xywatch/GoWatch/docs/1device选项.png

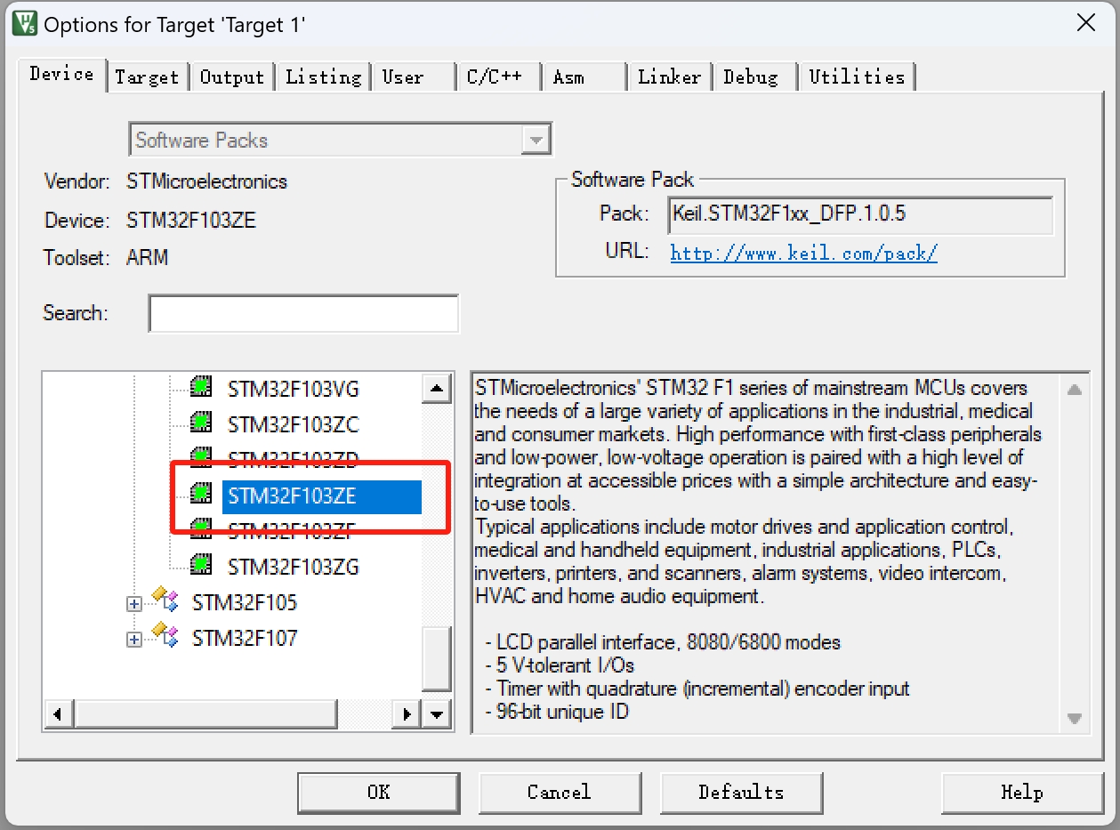
docs/1device选项.png
