xywatch/GoWatch/docs/2cc++.png

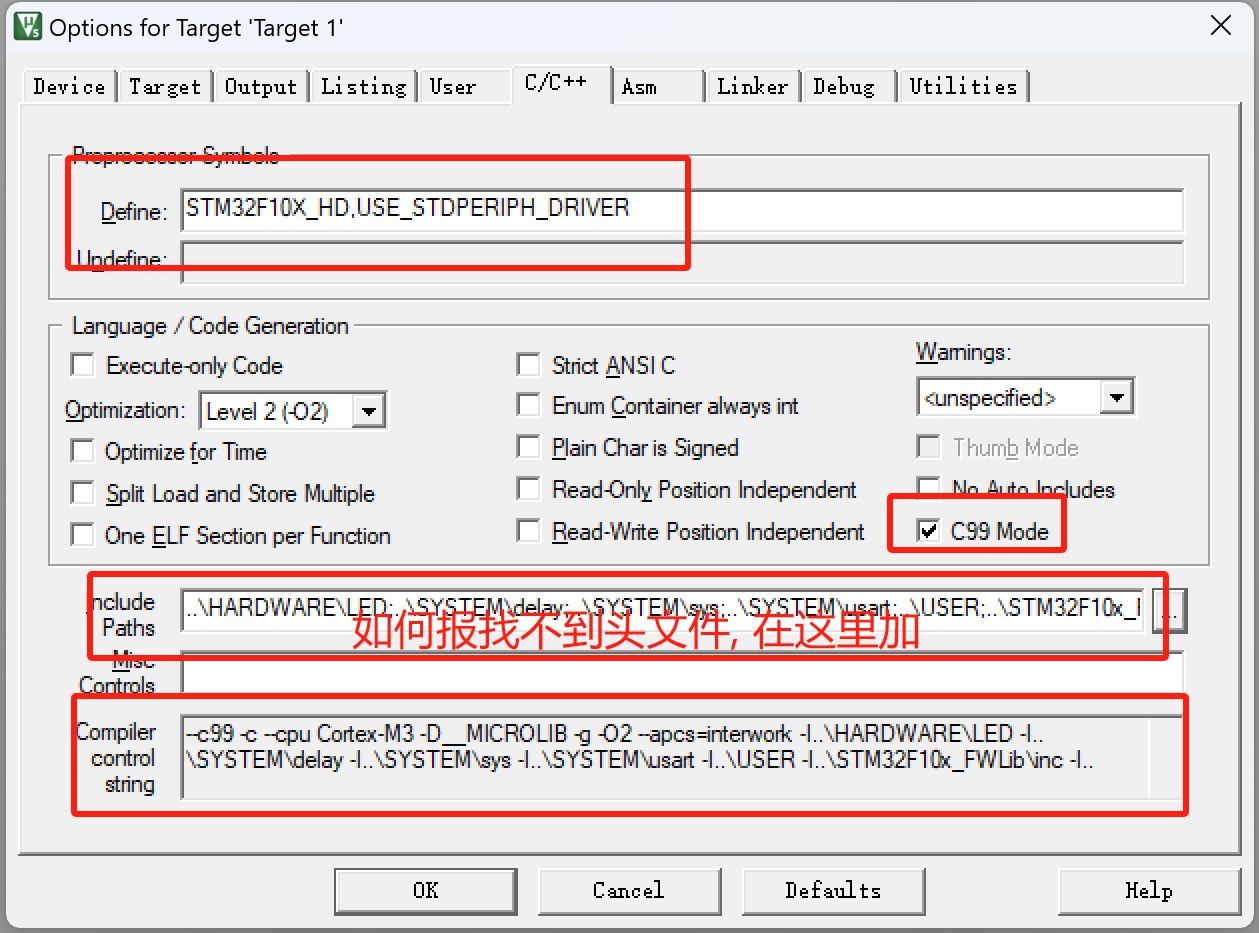
docs/2cc++.png
