xywatch/GoWatch/imgs/space/2.png

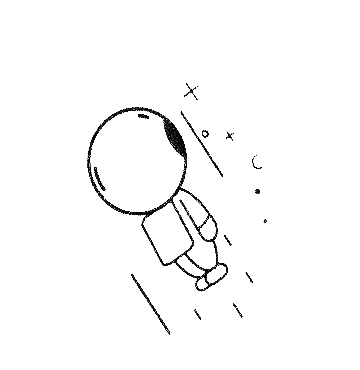
imgs/space/2.png
