xywatch/GoWatch/imgs/space/太空人.gif

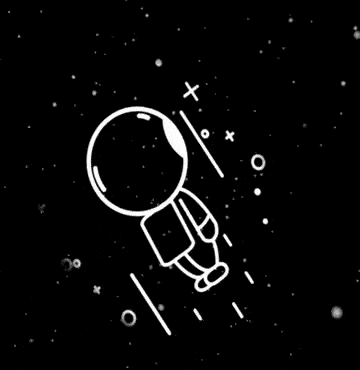
imgs/space/太空人.gif
