xywatch/GoWatch/APP/resources/resources.h

/*
 * Project: N|Watch
 * Author: Zak Kemble, contact@zakkemble.co.uk
 * Copyright: (C) 2013 by Zak Kemble
 * License: GNU GPL v3 (see License.txt)
 * Web: http://blog.zakkemble.co.uk/diy-digital-wristwatch/
 */

#ifndef RESOURCES_H_
#define RESOURCES_H_
#include "typedefs.h"
#include "english.h"

// extern const byte menu_default[];
extern const byte menu_alarm[];
extern const byte menu_stopwatch[];
extern const byte menu_torch[];
extern const byte menu_settings[];
extern const byte menu_diagnostic[];
extern const byte menu_exit[];
extern const byte selectbar_bottom[];
extern const byte selectbar_top[];

extern const char dowChars[];

extern const char days[7][BUFFSIZE_STR_DAYS];
extern const char months[12][BUFFSIZE_STR_MONTHS];

extern const byte step[];
extern const byte livesImg[];
extern const byte stopwatch[];

extern const byte dowImg[7][8];

extern const byte menu_tunemaker[];

extern const byte menu_timedate[];
extern const byte menu_sleep[];
extern const byte menu_sound[];
extern const byte menu_games[];
extern const byte menu_calendar[];
// extern const byte menu_calc[];
extern const byte menu_brightness[][128];
// extern const byte menu_LEDs[][128];
extern const byte menu_invert[];
extern const byte menu_anim[][128];
extern const byte menu_volume[][128];
extern const byte menu_rotate[];
extern const byte menu_display[];
extern const byte menu_sleeptimeout[];
extern const byte menu_double_tap[];
extern const byte menu_tilt_wrist[];
extern const byte menu_watchface[];

extern const byte usbIcon[];
extern const byte chargeIcon[];

extern const byte battIconEmpty[];
extern const byte battIconLow[];
extern const byte battIconHigh[];
extern const byte battIconFull[];

// 我的新增加图标
extern const byte menu_setfps[];
// Alarm icon
extern const byte smallFontAlarm[];

// 太空人
extern const byte space_image1[];
extern const byte space_image2[];
extern const byte space_image3[];
extern const byte space_image4[];
extern const byte space_image5[];
extern const byte space_image6[];
extern const byte space_image7[];
extern const byte space_image8[];
extern const byte space_image9[];
extern const byte space_image10[];

#define SMALLFONT_WIDTH 5
#define SMALLFONT_HEIGHT 8
extern const byte smallFont[][5];

/*
// Nwatch表盘 不要了, 字体不一致, 要统一
#define MIDFONT_WIDTH 19
#define MIDFONT_HEIGHT 24
extern const byte midFont[][57];

#define FONT_SMALL2_WIDTH 11
#define FONT_SMALL2_HEIGHT 16
extern const byte small2Font[][22];

#define FONT_COLON_WIDTH 6
#define FONT_COLON_HEIGHT 24
extern const byte colon[];
*/

// 微雪表盘
// 0-9
#define SMALLFONT_NUM_WIDTH 16
#define SMALLFONT_NUM_HEIGHT 16
extern const byte numFont16x16_weixue[11][32];

// 0-9
#define MIDFONT_NUM_WIDTH 16
#define MIDFONT_NUM_HEIGHT 32
extern const byte numFont16x32_weixue[11][64];

// Micro 5 宽高和weixue一样
extern const byte numFont16x16_micro5[11][32];
extern const byte numFont16x32_micro5[11][64];

extern const byte numFont16x16_tiny5[11][32];
extern const byte numFont16x32_tiny5[11][64];

extern const byte numFont16x16_jaro[11][32];
extern const byte numFont16x32_jaro[11][64];

extern const byte numFont16x16_revoluzia[11][32];
extern const byte numFont16x32_revoluzia[11][64];

// 表盘数量
#define WATCHFACE_COUNT 5

// 多个字体合并
extern const byte (*numFont16x16s[WATCHFACE_COUNT])[11][32];
extern const byte (*numFont16x32s[WATCHFACE_COUNT])[11][64];

#endif /* RESOURCES_H_ */
