xywatch/GoWatch/APP/watchface.c

/*
 * Project: N|Watch
 * Author: Zak Kemble, contact@zakkemble.co.uk
 * Copyright: (C) 2013 by Zak Kemble
 * License: GNU GPL v3 (see License.txt)
 * Web: http://blog.zakkemble.co.uk/diy-digital-wristwatch/
 */

#include "common.h"
#include "my_menu.h"
#include "bme280.h"
#include "altitude_display.h"

#define TIME_POS_Y 17
#define TICKER_GAP 4

// 8 * 16 = 128

typedef struct
{
    byte x;
    byte y;
    const byte *bitmap;
    byte w;
    byte h;
    byte offsetY;
    byte val;
    byte maxVal;
    bool moving;
} tickerData_t;

static display_t draw(void);
static void drawDate(void);
static display_t ticker(void);
static void drawTickerNum(tickerData_t *);
static void drawBattery(void);

byte seconds = 0;

// watch face
void watchface_normal()
{
    display_setDrawFunc(draw);
    buttons_setFuncs(altitude_open2, menu_select, my_menu_open2);
    showMeThenRun(NULL); // 设置打开过度动画，（不执行函数）
}

extern float DS3231_Temp;
extern BME280_Data bme280_data;

static display_t draw()
{
    // Draw date
    drawDate();

    // Draw time animated
    display_t busy;

    busy = ticker();

    // Draw battery icon
    drawBattery();
    byte x = 35;

#if COMPILE_STOPWATCH
    // Stopwatch icon
    if (stopwatch_active())
    {
        draw_bitmap(x, FRAME_HEIGHT - 8, stopwatch, 8, 8, NOINVERT, 0);
        x += 12;
    }

#endif 
	// Draw next alarm
    alarm_s nextAlarm;
    if(alarm_getNext(&nextAlarm))
    {
        time_s alarmTime;
        alarmTime.hour = nextAlarm.hour;
        alarmTime.mins = nextAlarm.min;
        alarmTime.ampm = CHAR_24;
        time_timeMode(&alarmTime, appConfig.timeMode);
        
        char buff[9];
        sprintf_P(buff, PSTR("%02hhu:%02hhu%c"), alarmTime.hour, alarmTime.mins, alarmTime.ampm);
        draw_string(buff, false, x, FRAME_HEIGHT - 8);

        x += (alarmTime.ampm == CHAR_24) ? 35 : 42;
        draw_bitmap(x, FRAME_HEIGHT - 8, dowImg[alarm_getNextDay()], 8, 8, NOINVERT, 0);
        x += 10;
    }

    char temp[8];
	// 显示温度
    // sprintf((char *)temp, "%0.1fC", bme280_data.T);
    // draw_string(temp, NOINVERT, FRAME_WIDTH - 35, FRAME_HEIGHT - 8);

    // 湿度
    sprintf((char *)temp, "%0.0f%%", bme280_data.H);
    draw_string(temp, NOINVERT, FRAME_WIDTH - (bme280_data.H > 0 ? 21 : 14), FRAME_HEIGHT - 8);

    return busy;
}

static void drawDate()
{
    // Get day string
    char day[BUFFSIZE_STR_DAYS];
    strcpy(day, days[timeDate.date.day]);

    // Get month string
    char month[BUFFSIZE_STR_MONTHS];
    strcpy(month, months[timeDate.date.month]);

    // Draw date
    char buff[BUFFSIZE_DATE_FORMAT];
    // sprintf_P(buff, PSTR(DATE_FORMAT), day, timeDate.date.date, month, timeDate.date.year);
    sprintf(buff, "%02d-%02d-%02d %s", timeDate.date.year, timeDate.date.month + 1, timeDate.date.date, day);

    u8 x = 0;
    // 显示温度
    if (bme280_data.T > 0)
    {
        draw_string(buff, false, x, 0);
        char buff2[8];
        sprintf((char *)buff2, "%0.1fC", bme280_data.T);
        draw_string(buff2, NOINVERT, FRAME_WIDTH - 35, 0);
    }
    else {
        draw_string_center(buff, false, x, 127, 0);
    }
}

static display_t ticker()
{
    static byte yPos;
    static byte yPos_secs;
    static bool moving = false;
    static bool moving2[5];

    static byte hour2;
    static byte mins;
    static byte secs;

    byte midFontHeight;
    byte midFontWidth;
    byte smallFontHeight;
    byte smallFontWidth;
    byte timePosX = 0;
    byte timePosY;

    midFontHeight = MIDFONT_NUM_HEIGHT;
    midFontWidth = MIDFONT_NUM_WIDTH;
    smallFontHeight = SMALLFONT_NUM_HEIGHT;
    smallFontWidth = SMALLFONT_NUM_WIDTH;
    timePosY = 17;

    if (appConfig.animations)
    {
        if (timeDate.time.secs != secs)
        {
            yPos = 0;
            yPos_secs = 0;
            moving = true;

            moving2[0] = div10(timeDate.time.hour) != div10(hour2);
            moving2[1] = mod10(timeDate.time.hour) != mod10(hour2);
            moving2[2] = div10(timeDate.time.mins) != div10(mins);
            moving2[3] = mod10(timeDate.time.mins) != mod10(mins);
            moving2[4] = div10(timeDate.time.secs) != div10(secs);

            // moving2[3] = 1;

            // memcpy(&timeDateLast, &timeDate, sizeof(timeDate_s));
            hour2 = timeDate.time.hour;
            mins = timeDate.time.mins;
            secs = timeDate.time.secs;
        }

        // 之前height是 16 24
        // 改成了 16 32
        // TICKER_GAP 有什么用? 秒和时针的结束动画错开, 时晚4
        if (moving)
        {
            if (yPos <= 3)
            {
                yPos++;
            }
            else if (yPos <= 6)
            {
                yPos += 3;
            }
            else if (yPos <= 16)
            {
                yPos += 5;
            }
            else if (yPos <= midFontHeight - 3)
            { // 22 前快后慢
                yPos += 3;
            }
            else if (yPos <= midFontHeight + TICKER_GAP)
            { // 24 + TICKER_GAP, 如果还用24会卡顿
                yPos++;
            }

            if (yPos >= midFontHeight + TICKER_GAP)
            {
                yPos = 255;
            }

            if (yPos_secs <= 1)
            {
                yPos_secs++;
            }
            else if (yPos_secs <= smallFontHeight - 3)
            {
                yPos_secs += 3;
            }
            else if (yPos_secs <= smallFontHeight + TICKER_GAP)
            {
                yPos_secs++;
            }

            if (yPos_secs >= smallFontHeight + TICKER_GAP)
            {
                yPos_secs = 255;
            }

            if (yPos_secs > smallFontHeight + TICKER_GAP && yPos > midFontHeight + TICKER_GAP)
            {
                yPos = 0;
                yPos_secs = 0;
                moving = false;
                memset(moving2, false, sizeof(moving2));
            }
        }
    }
    else
    {
        yPos = 0;
        yPos_secs = 0;
        moving = false;
        memset(moving2, false, sizeof(moving2));
    }

    tickerData_t data;

    // Set new font data for hours and minutes
    data.w = midFontWidth;
    data.h = midFontHeight;

    byte *colon_big;
    byte *colon_small;
    data.bitmap = (const byte *)numFont16x32s[appConfig.watchface];
    colon_big = (byte *)(*numFont16x32s[appConfig.watchface])[10];

    data.y = timePosY;
    data.offsetY = yPos;

    // Hours
    data.x = timePosX;
    data.val = div10(timeDate.time.hour);
    data.maxVal = 2;
    data.moving = moving2[0];
    drawTickerNum(&data);

    data.x += 16;
    data.val = mod10(timeDate.time.hour);
    data.maxVal = 9;
    data.moving = moving2[1];
    drawTickerNum(&data);

    data.x += 16;

    // 时与分的冒号
    draw_bitmap(data.x, timePosY, colon_big, midFontWidth, midFontHeight, NOINVERT, 0);

    // Minutes
    data.x += 16;
    data.val = div10(timeDate.time.mins);
    data.maxVal = 5;
    data.moving = moving2[2];
    drawTickerNum(&data);

    data.x += 16;
    data.val = mod10(timeDate.time.mins);
    data.maxVal = 9;
    data.moving = moving2[3];
    drawTickerNum(&data);

    data.x += 16;
    // Seconds
    data.y += 16;

    data.w = smallFontWidth;
    data.h = smallFontHeight;

    data.bitmap = (const byte *)numFont16x16s[appConfig.watchface];
    colon_small = (byte *)(*numFont16x16s[appConfig.watchface])[10];

    if (millis() % 1000 >= 500) // 0.5s 1秒分成两断, 后半秒显示, 前半秒隐藏
    {
        draw_bitmap(data.x, data.y, colon_small, smallFontWidth, smallFontHeight, NOINVERT, 0);
    }

    data.x += 16;
    data.offsetY = yPos_secs;
    data.val = div10(timeDate.time.secs);
    data.maxVal = 5;
    data.moving = moving2[4];
    drawTickerNum(&data);

    data.x += 16;
    data.val = mod10(timeDate.time.secs);
    data.maxVal = 9;
    data.moving = moving;
    drawTickerNum(&data);

    // Draw AM/PM character
    char tmp[2];
    tmp[0] = timeDate.time.ampm;
    tmp[1] = 0x00;
    draw_string(tmp, false, 104, 20);

    return (moving ? DISPLAY_BUSY : DISPLAY_DONE);
}

static void drawTickerNum(tickerData_t *data)
{
    byte arraySize = (data->w * data->h) / 8;
    byte yPos = data->offsetY;
    const byte *bitmap = &data->bitmap[data->val * arraySize];
    byte x = data->x;
    byte y = data->y;

    if (!data->moving || yPos == 0 || yPos == 255)
    {
        draw_bitmap(x, y, bitmap, data->w, data->h, NOINVERT, 0);
    }
    else
    {
        byte prev = data->val - 1;

        if (prev == 255)
        {
            prev = data->maxVal;
        }

        draw_bitmap(x, y, bitmap, data->w, data->h, NOINVERT, yPos - data->h - TICKER_GAP);
        draw_bitmap(x, y, &data->bitmap[prev * arraySize], data->w, data->h, NOINVERT, yPos);
    }
}

float BatteryVol;

// 电池电量百分比计算
static int calcBatteryPercentage(float voltage) {
    // 锂电池电压范围
    const float VBAT_MAX = 4.2f;  // 满电电压
    const float VBAT_MIN = 3.2f;  // 最低电压
    const float VBAT_FULL = 4.15f; // 认为完全充满的电压
    
    // 电压限幅
    if(voltage > VBAT_MAX) voltage = VBAT_MAX;
    if(voltage < VBAT_MIN) voltage = VBAT_MIN;
    
    // 非线性映射计算电量百分比
    float percentage;
    if(voltage >= VBAT_FULL) {
        percentage = 100.0f;
    }
    else if(voltage >= 3.9f) { // 4.15V-3.9V 映射到 100%-80%
        percentage = 80.0f + (voltage - 3.9f) * 20.0f / (VBAT_FULL - 3.9f);
    }
    else if(voltage >= 3.7f) { // 3.9V-3.7V 映射到 80%-55%
        percentage = 55.0f + (voltage - 3.7f) * 25.0f / 0.2f;
    }
    else if(voltage >= 3.5f) { // 3.7V-3.5V 映射到 55%-30%
        percentage = 30.0f + (voltage - 3.5f) * 25.0f / 0.2f;
    }
    else { // 3.5V-3.2V 映射到 30%-0%
        percentage = (voltage - VBAT_MIN) * 30.0f / 0.3f;
    }
    
    return (int)(percentage + 0.5f); // 四舍五入
}

static void drawBattery()
{
    int bat;
    char ad[5];
    const byte *battIcon;

    // 根据电量百分比选择电池图标
    bat = calcBatteryPercentage(BatteryVol);
    
    if (bat < 10) {
        battIcon = battIconEmpty;
    }
    else if (bat < 30) {
        battIcon = battIconLow;
    }
    else if (bat < 60) {
        battIcon = battIconHigh;
    }
    else if (bat < 90) {
        battIcon = battIconHigh;  // 可以添加更多图标
    }
    else {
        battIcon = battIconFull;
    }

    // 绘制电池图标
    draw_bitmap(0, FRAME_HEIGHT - 8, battIcon, 16, 8, NOINVERT, 0);

    if (bat >= 100) {
        bat = 99;
    }

    // 显示电量百分比
    sprintf((char *)ad, "%d", bat);
    draw_string(ad, NOINVERT, 18, FRAME_HEIGHT - 8);
}
