xywatch/GoWatch/APP/stopwatch.c

/*
 * Project: N|Watch
 * Author: Zak Kemble, contact@zakkemble.co.uk
 * Copyright: (C) 2013 by Zak Kemble
 * License: GNU GPL v3 (see License.txt)
 * Web: http://blog.zakkemble.co.uk/diy-digital-wristwatch/
 */

#include "common.h"

#if COMPILE_STOPWATCH

typedef enum
{
    STATE_STOPPED = 0,
    STATE_TIMING
} stopwatch_state_t;

static stopwatch_state_t state;
static ulong timer;
static millis_t lastMS;

static bool btnReset(void);
static bool btnStartStop(void);
static bool btnExit(void);
static display_t draw(void);

void stopwatch_open()
{
    // menu_close();

    display_setDrawFunc(draw);
    buttons_setFuncs(btnReset, btnStartStop, btnExit);
    showMeThenRun(NULL); // 打开动画动画过度
}

bool stopwatch_active()
{
    return (state == STATE_TIMING);
}

void stopwatch_update()
{
    if (state == STATE_TIMING)
    {
        millis_t now = millis();
        timer = timer + now - lastMS;
        lastMS = now;

        if (timer > 359999999)
        { // 99 hours, 59 mins, 59 secs, 999 ms
            timer = 359999999;
        }
    }
}

static bool btnReset()
{
    timer = 0;
    lastMS = millis();
    return true;
}

static bool btnStartStop()
{
    if (state == STATE_TIMING)
    {
        state = STATE_STOPPED;
        //		pwrmgr_setState(PWR_ACTIVE_STOPWATCH, PWR_STATE_NONE);
    }
    else if (state == STATE_STOPPED)
    {
        state = STATE_TIMING;
        //		pwrmgr_setState(PWR_ACTIVE_STOPWATCH, PWR_STATE_IDLE);
    }

    lastMS = millis();
    return true;
}

static bool btnExit()
{
    // animation_start(display_load, ANIM_MOVE_OFF);
    exitMeThenRun(back);
    return true;
}

#define TIME_POS_X 1
#define TIME_POS_Y 20

static display_t draw()
{
    // Draw battery icon
    // drawBattery();

    byte num1;
    byte num2;
    byte num3;
    ulong timer1 = timer; // 模拟一秒的时间
    ulong secs = timer1 / 1000;

    if (timer1 < 3600000)
    {
        num3 = (timer1 % 1000) / 10; // ms
        num2 = secs % 60;            // secs
        num1 = secs / 60;            // mins
    }
    else
    {
        num3 = secs % 60;        // secs
        num2 = (secs / 60) % 60; // mins
        num1 = (secs / 3600);    // hours
    }

    char x = 8;
    // 分
    draw_bitmap(x, TIME_POS_Y, (const byte*)((*numFont16x32s[appConfig.watchface])[div10(num1)]), MIDFONT_NUM_WIDTH, MIDFONT_NUM_HEIGHT, NOINVERT, 0);
    x += 16;
    draw_bitmap(x, TIME_POS_Y, (const byte*)((*numFont16x32s[appConfig.watchface])[mod10(num1)]), MIDFONT_NUM_WIDTH, MIDFONT_NUM_HEIGHT, NOINVERT, 0);
    x += 16;
    // :
    draw_bitmap(x, TIME_POS_Y, (const byte*)((*numFont16x32s[appConfig.watchface])[10]), MIDFONT_NUM_WIDTH, MIDFONT_NUM_HEIGHT, NOINVERT, 0);
    x += 16;
    // 秒
    draw_bitmap(x, TIME_POS_Y, (const byte*)((*numFont16x32s[appConfig.watchface])[div10(num2)]), MIDFONT_NUM_WIDTH, MIDFONT_NUM_HEIGHT, NOINVERT, 0);
    x += 16;
    draw_bitmap(x, TIME_POS_Y, (const byte*)((*numFont16x32s[appConfig.watchface])[mod10(num2)]), MIDFONT_NUM_WIDTH, MIDFONT_NUM_HEIGHT, NOINVERT, 0);
    x += 16;
    // 秒2
    draw_bitmap(x, TIME_POS_Y + 16, (const byte*)((*numFont16x16s[appConfig.watchface])[div10(num3)]), SMALLFONT_NUM_WIDTH, SMALLFONT_NUM_HEIGHT, NOINVERT, 0);
    x += 16;
    draw_bitmap(x, TIME_POS_Y + 16, (const byte*)((*numFont16x16s[appConfig.watchface])[mod10(num3)]), SMALLFONT_NUM_WIDTH, SMALLFONT_NUM_HEIGHT, NOINVERT, 0);
    x += 16;

    // Draw time
    draw_string(time_timeStr(), NOINVERT, 48, 0);

    return DISPLAY_BUSY;
}

#endif
