xywatch/GoWatch/APP/gui_log_console.h

#ifndef _GUI_LOG_CONSOLE_H_
#define _GUI_LOG_CONSOLE_H_

#include "sys.h"
#include "stdbool.h"

typedef struct
{
	char str_buff[20];
} STRBUFF;

void console_loop_show(void);
void console_log(unsigned short time_delay, char *fmt, ...);
bool up_line(void);
bool down_line(void);

#endif
